sadekbaroudi/vik/pcb/ec11-evqwgd001/README.md

# ec11 evqwgd001 vik module

## Overview

This is a simple EC11 and EVQWGD001 vik module. It has support for 4 upwards facing SK6812 mini-e leds, in case you want to add a little pizzazz to your encoder.

Please note that this PCB does **not** support the click, only rotation of the encoder.

## Fabrication and BOM

For PCB fabrication, you can use the files in the production folder.

* gerbers.zip - the file used to fabricate the pcb
* bom.csv - used for PCBA. You can also use the part numbers in this file to look up the exact parts as [lcsc.com](https://lcsc.com)
* positions.csv - used for PCBA

Using the 3 files above, this has been tested at [jlcpcb.com](https://jlcpcb.com)

## VIK module certification

| Category | Classification | Response |
| --- | --- | --- |
| FPC connector | Required | :heavy_check_mark: |
| Breakout pins | Recommended | :x: |
| Uses: SPI | Optional | :x: |
| SPI used for SPI only | Strongly recommended | N/A |
| Uses: I2C | Optional | :x: |
| I2C used for I2C only | Strongly Recommended | :x: |
| I2C pull ups | Required | N/A |
| Uses: RGB | Optional | :heavy_check_mark: |
| Uses: Extra GPIO 1 | Optional | :heavy_check_mark: |
| Uses: Extra GPIO 2 | Optional | :heavy_check_mark: |
| Standard PCB Size/Mount | Strongly recommended | :x: |

## PCB images

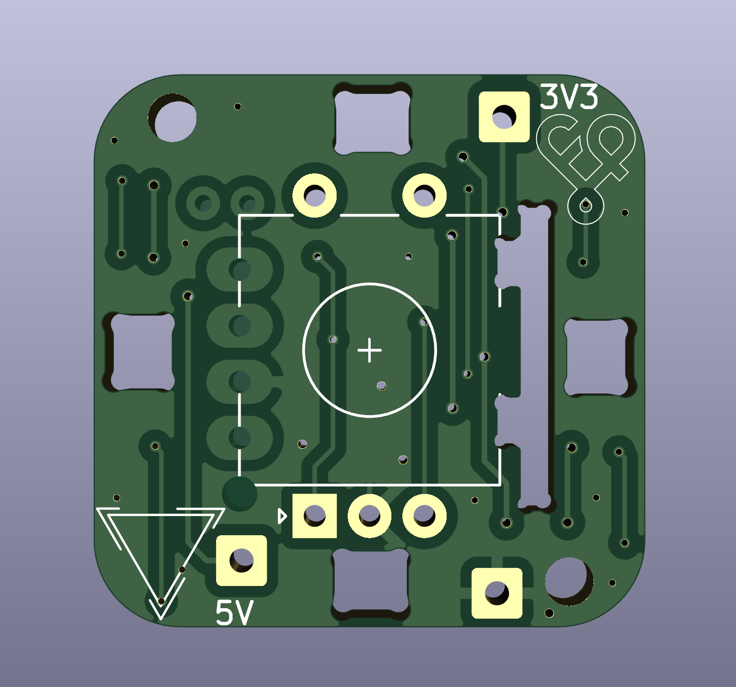
[picture p56: pcb/ec11-evqwgd001/images/ec11-evqwgd001-module-front.png]
pcb front


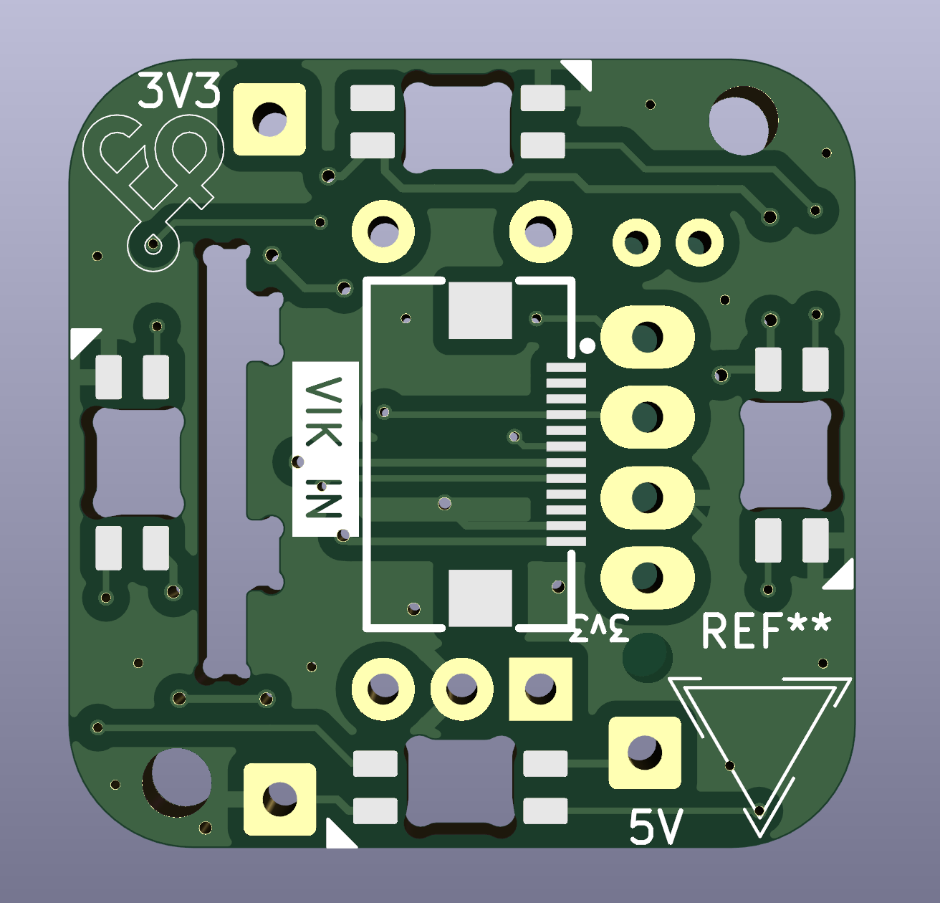
[picture p57: pcb/ec11-evqwgd001/images/ec11-evqwgd001-module-back.png]
pcb back
