sadekbaroudi/vik/images/vik-i2c-dnp.png

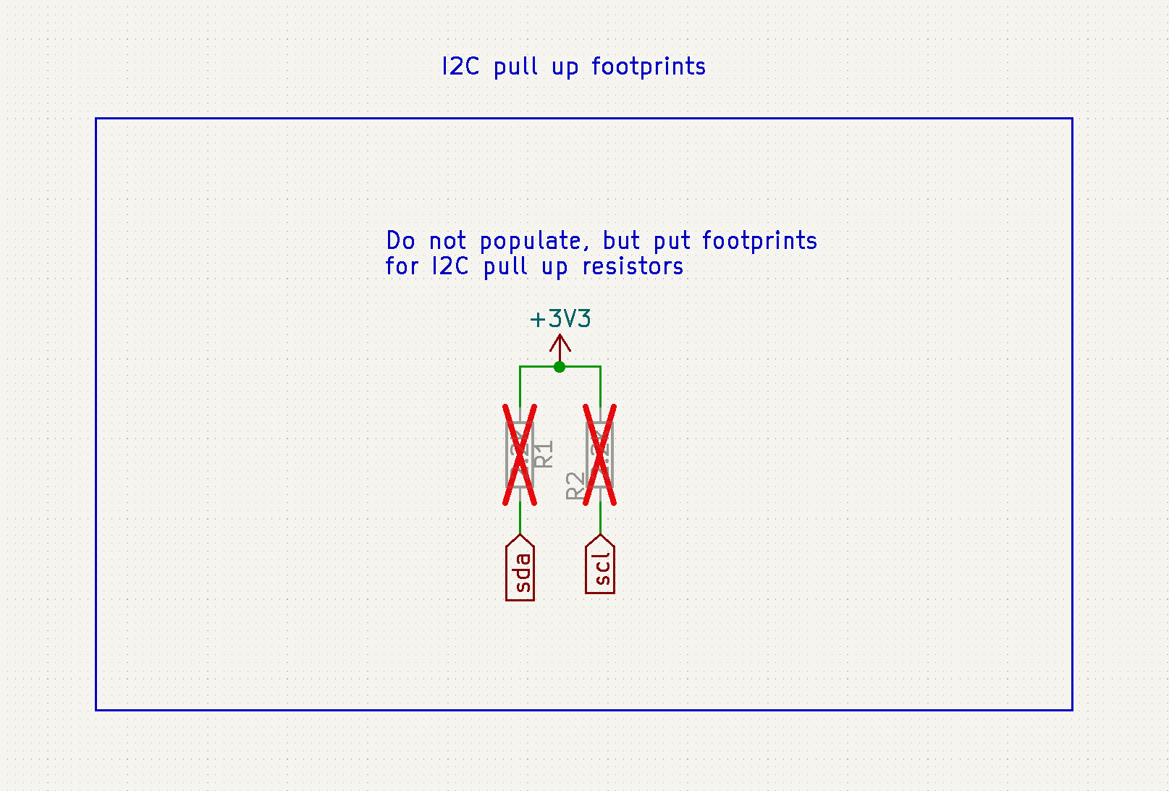
images/vik-i2c-dnp.png
