sadekbaroudi/vik/pcb/gc9a01/images/gc9a01-module-back.png

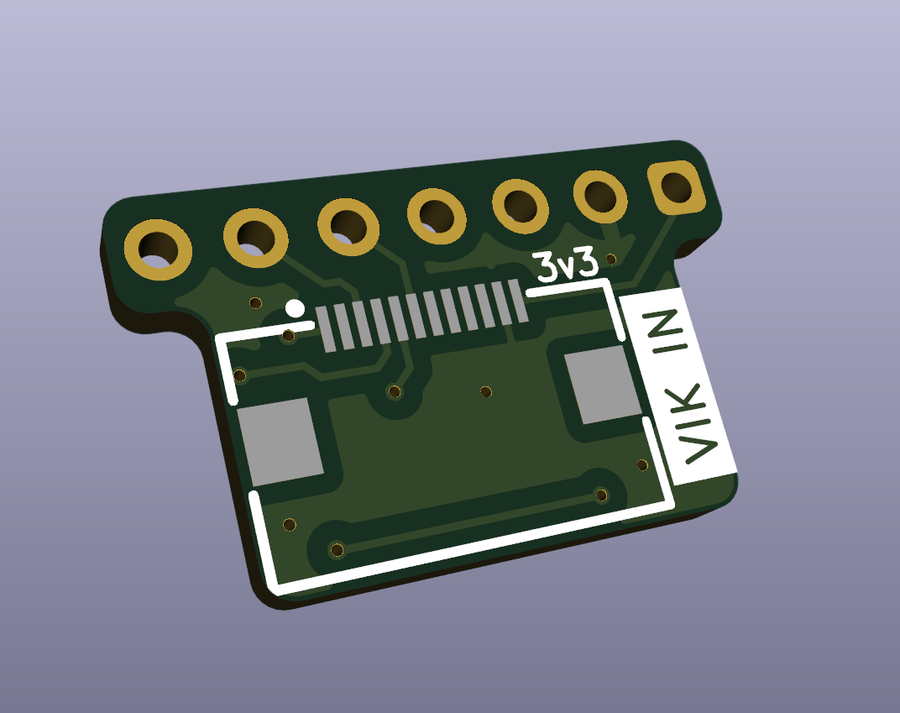
pcb/gc9a01/images/gc9a01-module-back.png
