sadekbaroudi/vik/pcb/haptic/images/haptic-module-back.png

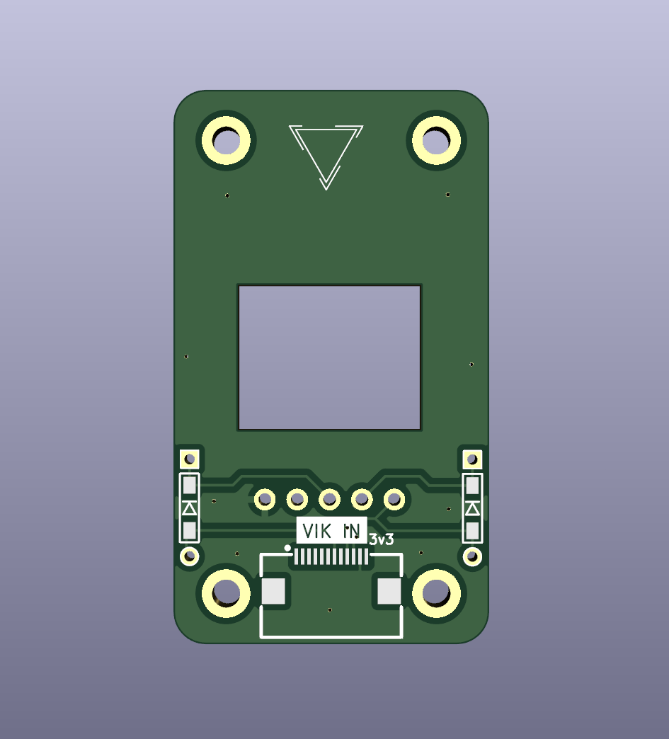
pcb/haptic/images/haptic-module-back.png
