sadekbaroudi/vik/pcb/haptic/images/haptic-module-front.png

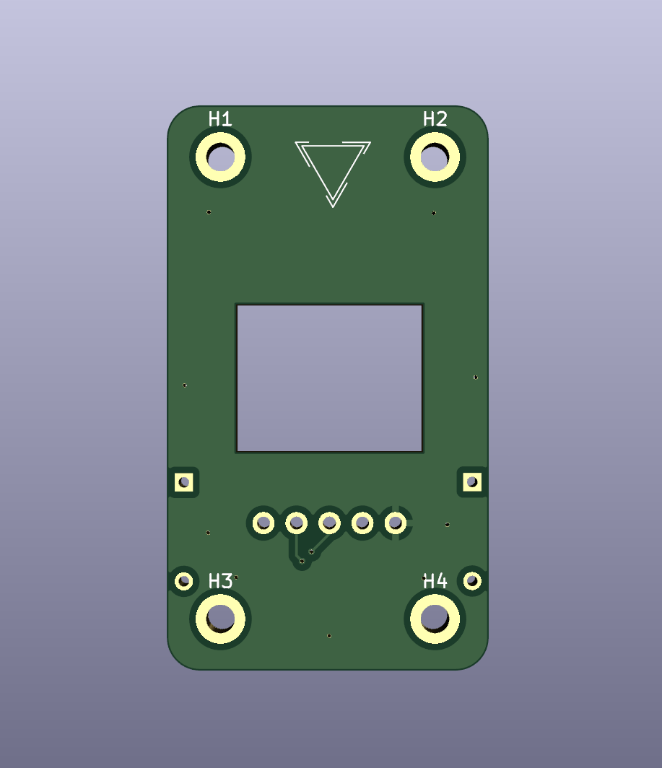
pcb/haptic/images/haptic-module-front.png
