sadekbaroudi/vik/pcb/ili9341v/images/1.8_SPI_Size.png

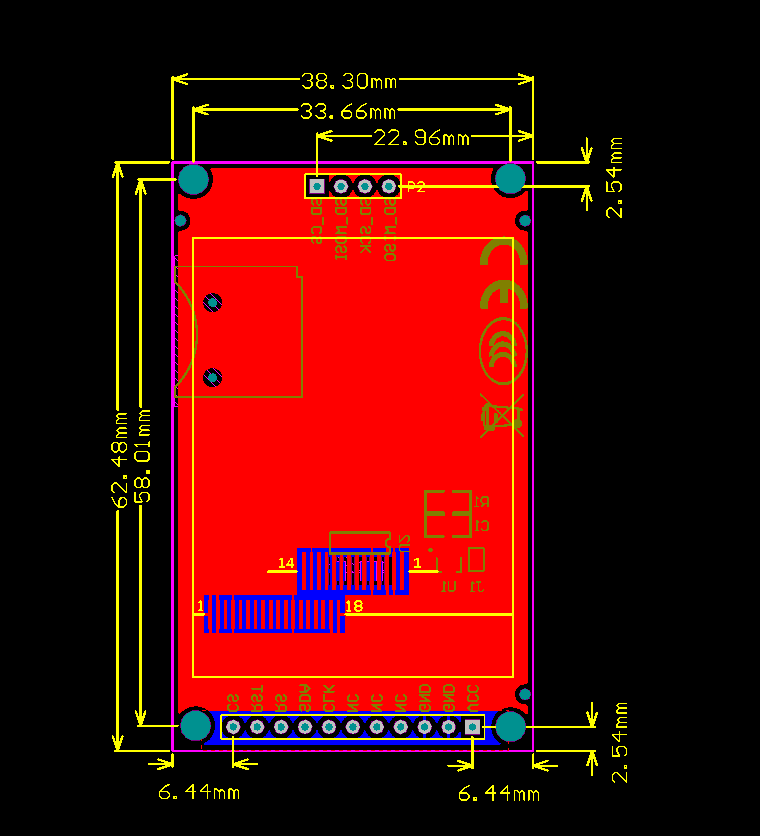
pcb/ili9341v/images/1.8_SPI_Size.png
