sadekbaroudi/vik/pcb/ili9341v/images/2.0inch_SPI_MAR2001_Size.png

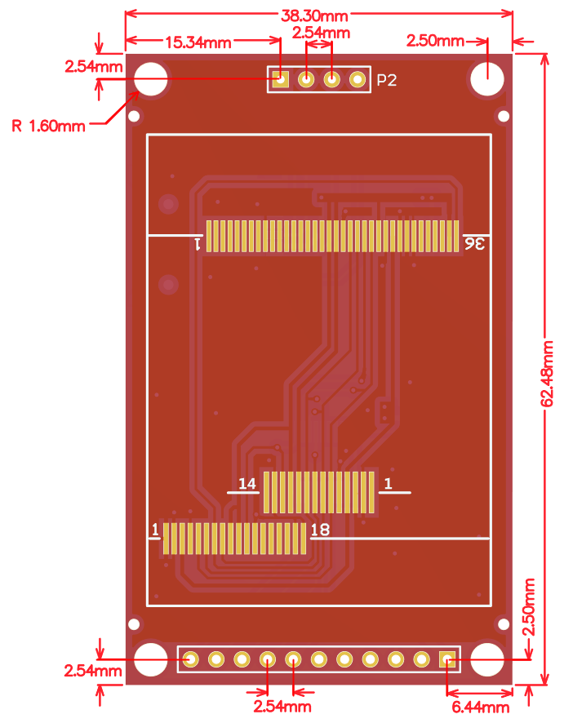
pcb/ili9341v/images/2.0inch_SPI_MAR2001_Size.png
