sadekbaroudi/vik/pcb/ili9341v/images/2.2inch_Arduino_SPI_Size.png

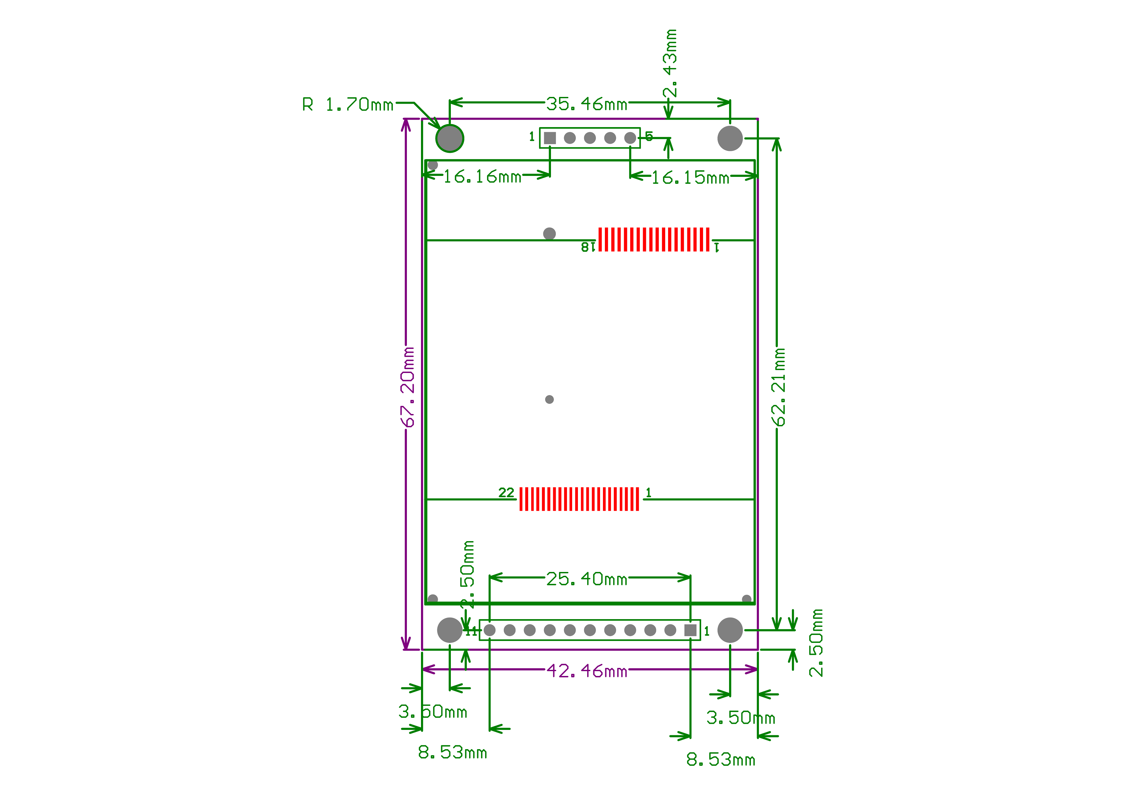
pcb/ili9341v/images/2.2inch_Arduino_SPI_Size.png
