sadekbaroudi/vik/pcb/ili9341v/images/3.5inch_SPI_Size.png

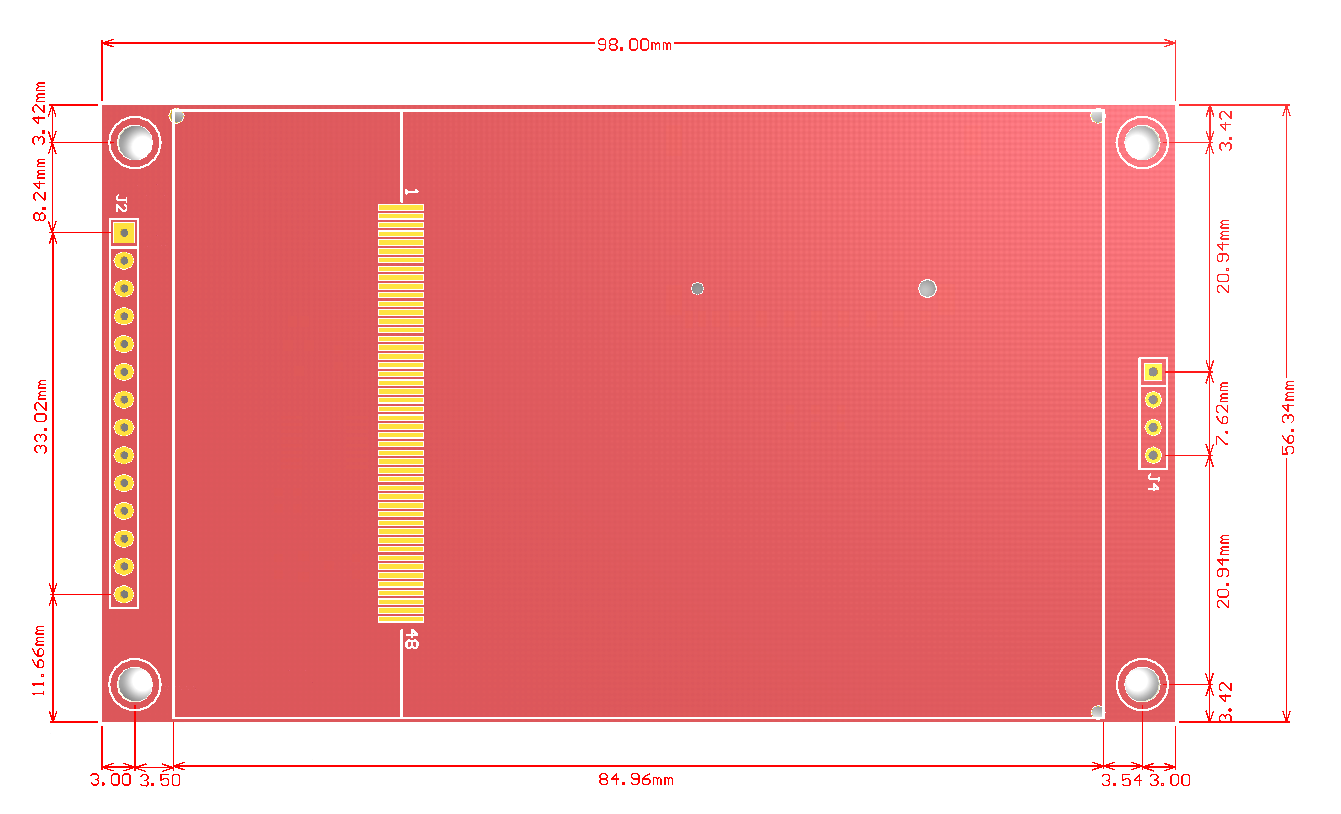
pcb/ili9341v/images/3.5inch_SPI_Size.png
