sadekbaroudi/vik/pcb/ili9341v/images/4.0inch_SPI_size.png

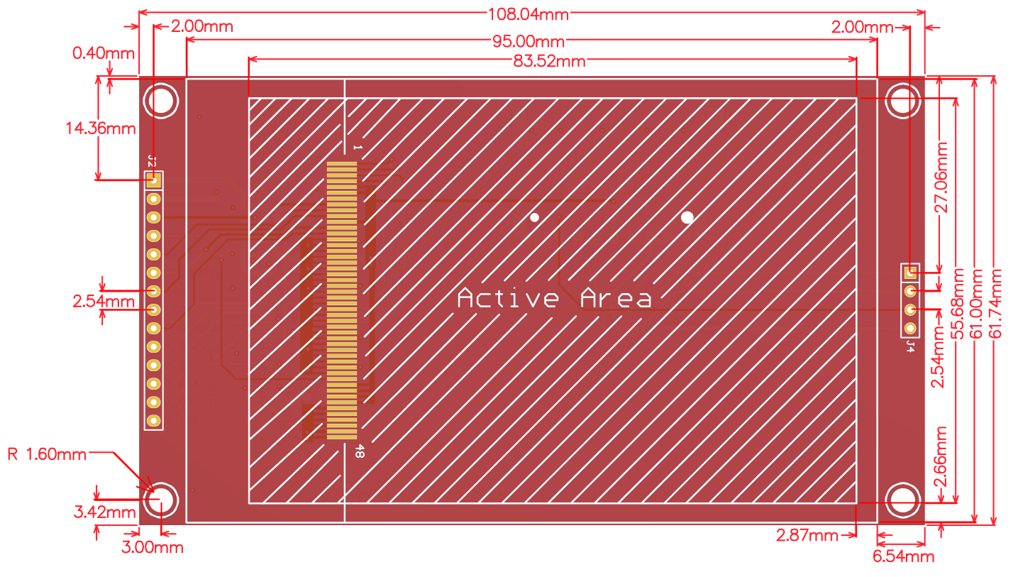
pcb/ili9341v/images/4.0inch_SPI_size.png
