sadekbaroudi/vik/pcb/per56-pmw3360-leds/images/per56-pmw3360-leds-module-front.png

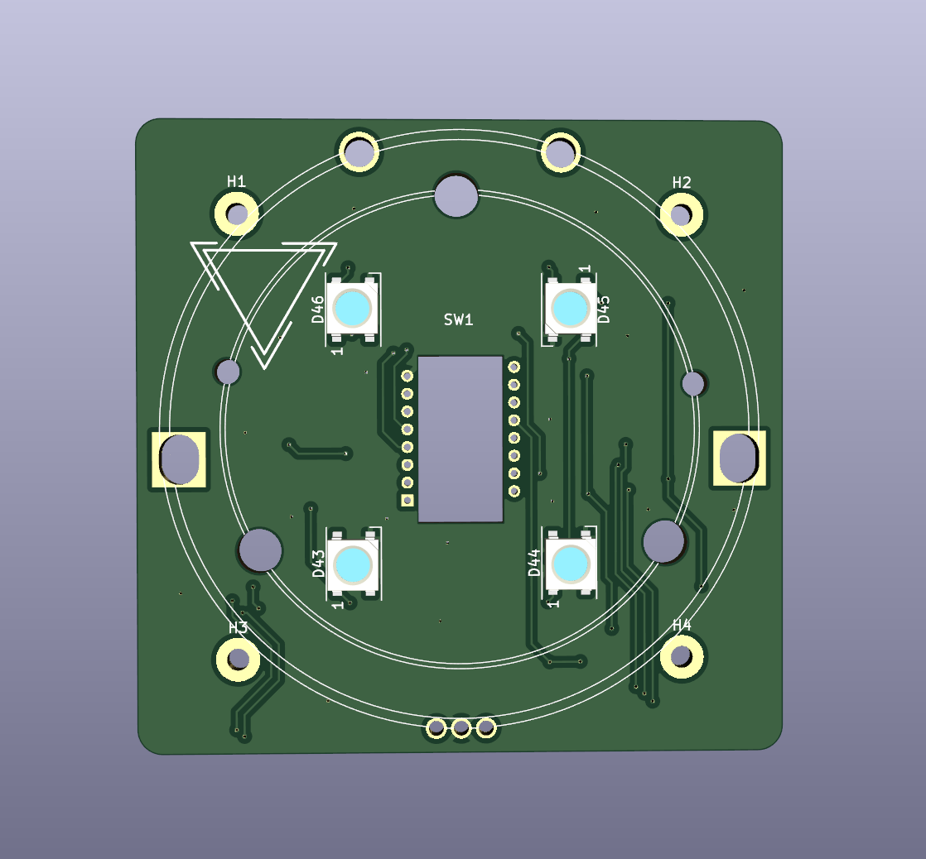
pcb/per56-pmw3360-leds/images/per56-pmw3360-leds-module-front.png
