sadekbaroudi/vik/pcb/vik-playground/images/vik-playground-back.png

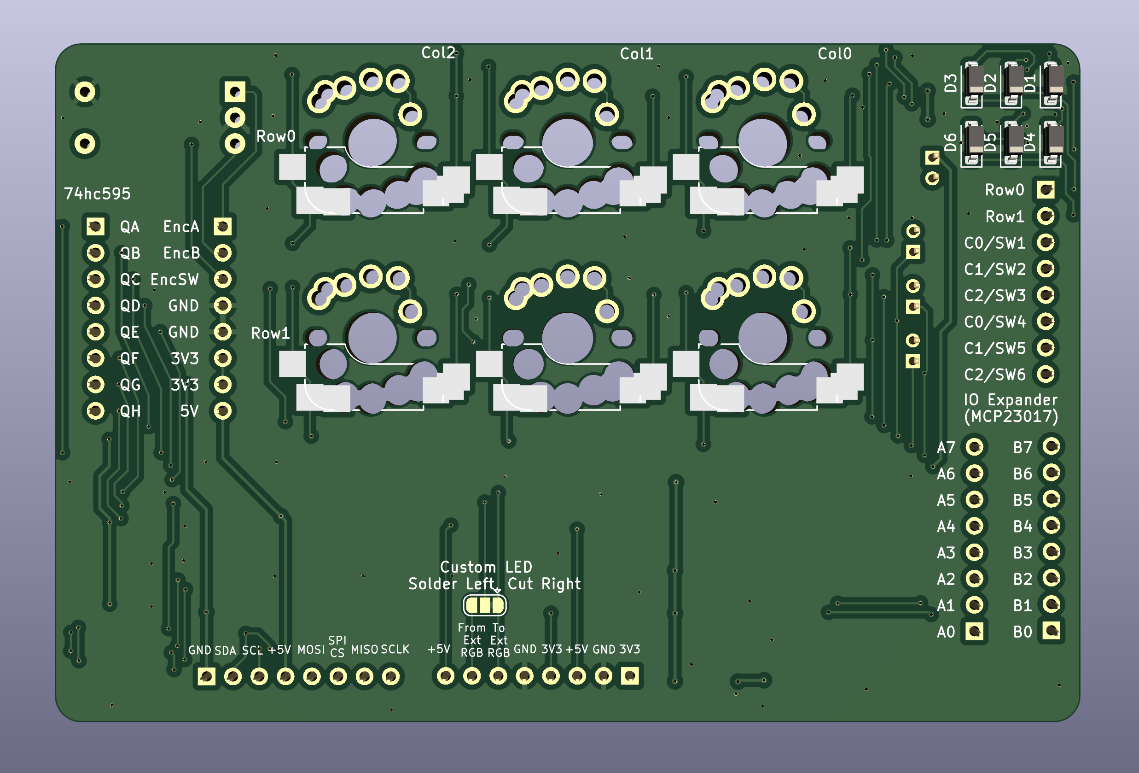
pcb/vik-playground/images/vik-playground-back.png
