sadekbaroudi/vik/pcb/vik-playground/images/vik-playground-front.png

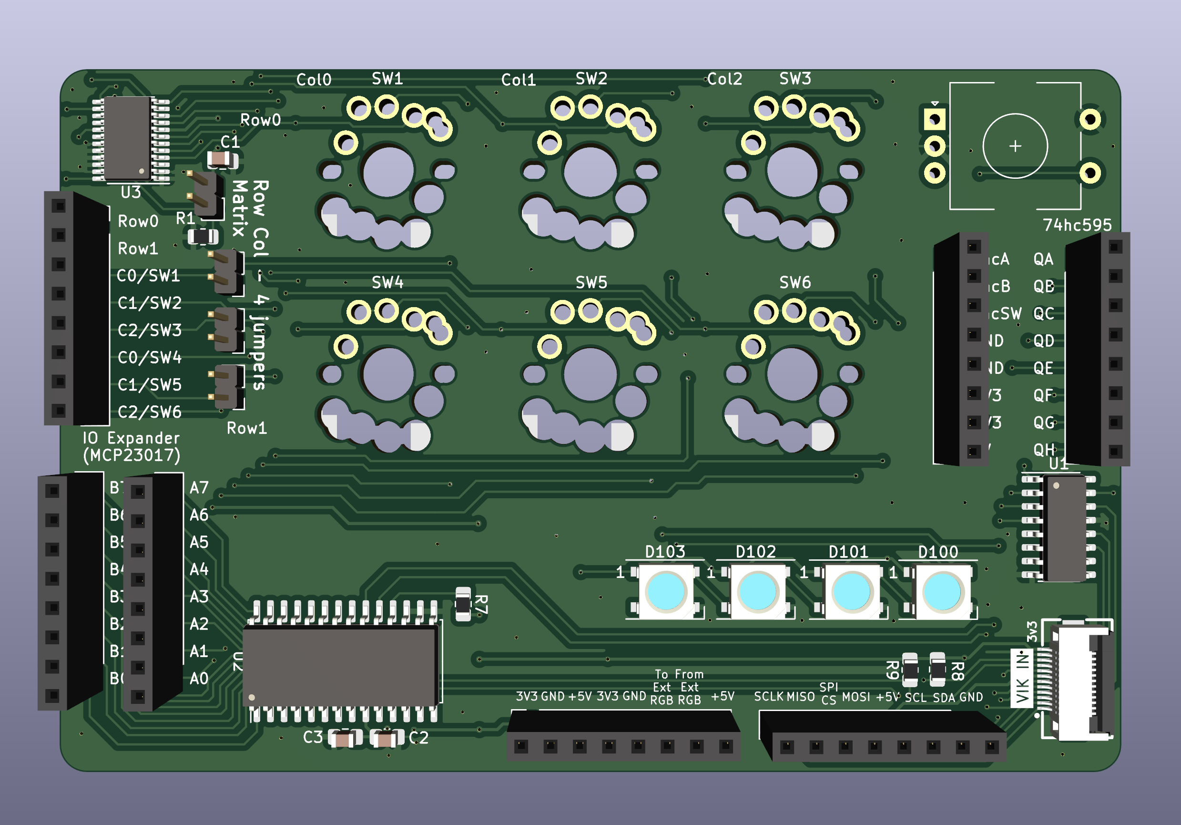
pcb/vik-playground/images/vik-playground-front.png
