sadekbaroudi/vik/pcb/vik-universal/jumper-input-output-matrix/images/vik-universal-back.png

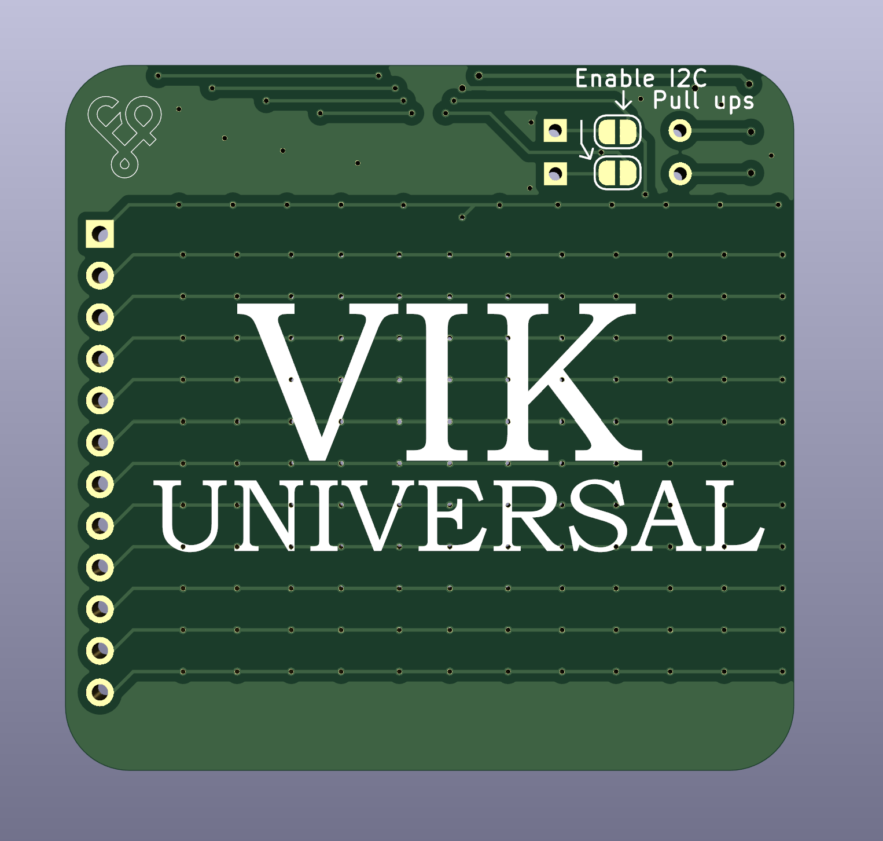
pcb/vik-universal/jumper-input-output-matrix/images/vik-universal-back.png
