sadekbaroudi/vik/pcb/vik-universal/jumper-input-output-matrix/images/vik-universal-front.png

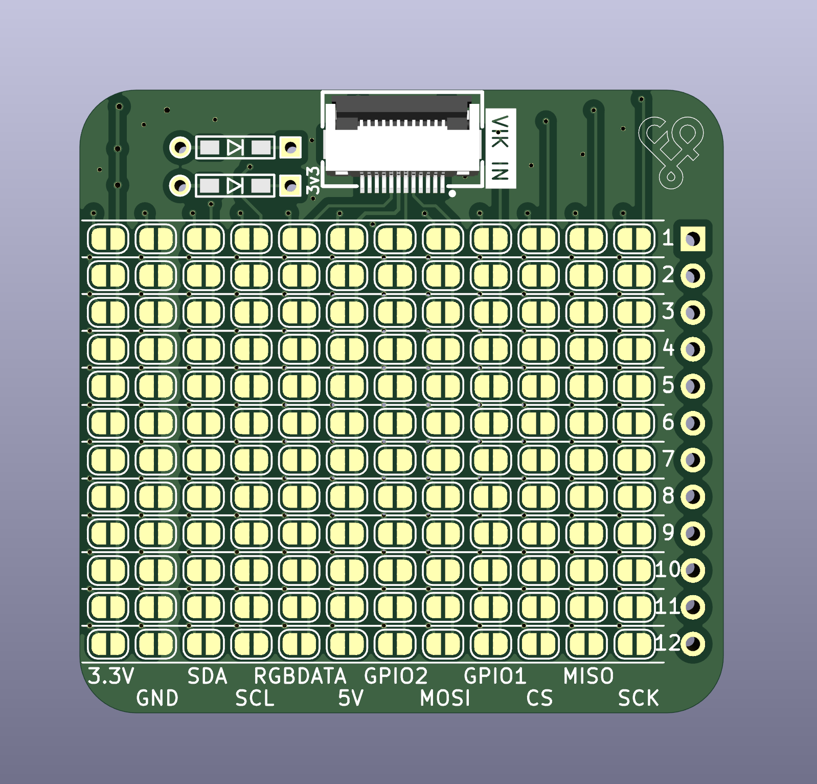
pcb/vik-universal/jumper-input-output-matrix/images/vik-universal-front.png
