sadekbaroudi/vik/pcb/weact-st7735/images/weact-st7735-module-front.png

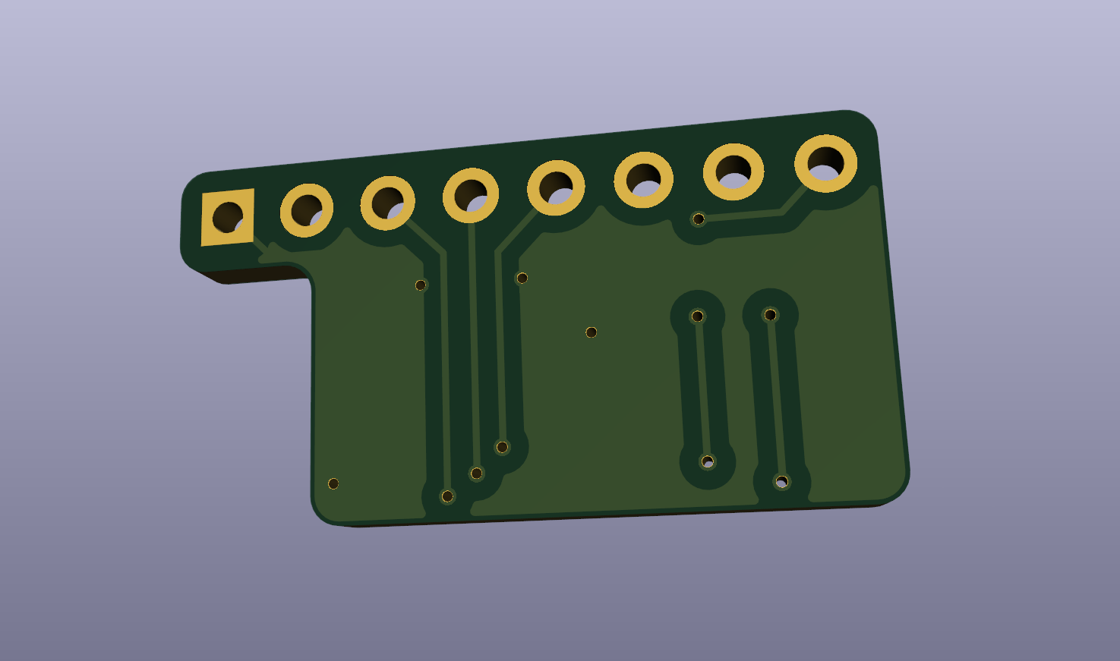
pcb/weact-st7735/images/weact-st7735-module-front.png
