sadekbaroudi/vik/pcb/niceview/horizontal-fpc/production/bom.csv

Designator | Footprint | Quantity | Value | LCSC Part #
Display1 | nice_view | 1 | nice!view
J1 | vik-module-connector-horizontal | 1 | ~ | C479750
