sadekbaroudi/vik/pcb/joysticks/images/joycon-wiring.jpg

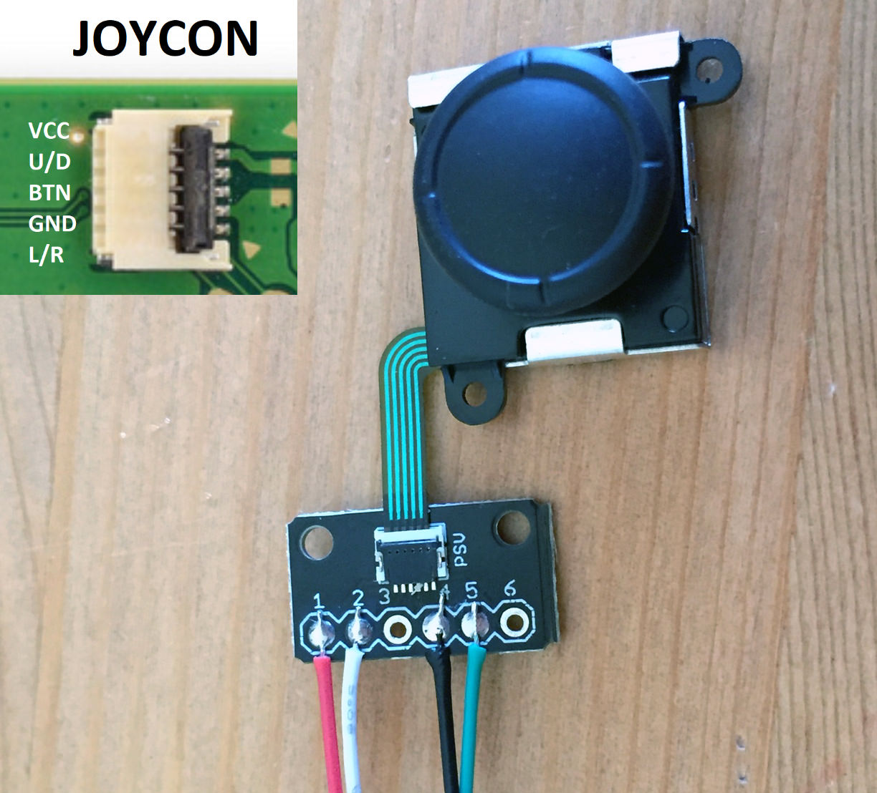
pcb/joysticks/images/joycon-wiring.jpg
